sle118/LORA_Sensor/transmitter/334974604_918132536177839_5854289335399050512_n.jpg

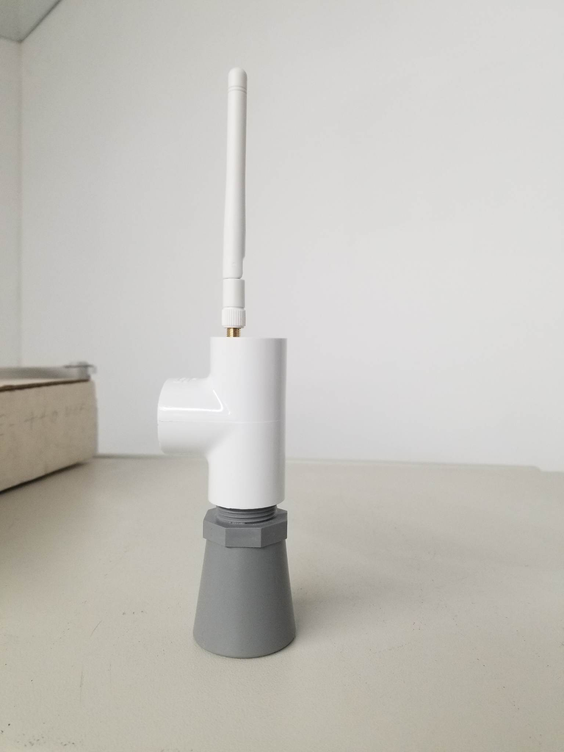
transmitter/334974604_918132536177839_5854289335399050512_n.jpg
