sle118/LORA_Sensor/transmitter/335561218_125201400374179_6329099118651229708_n.jpg

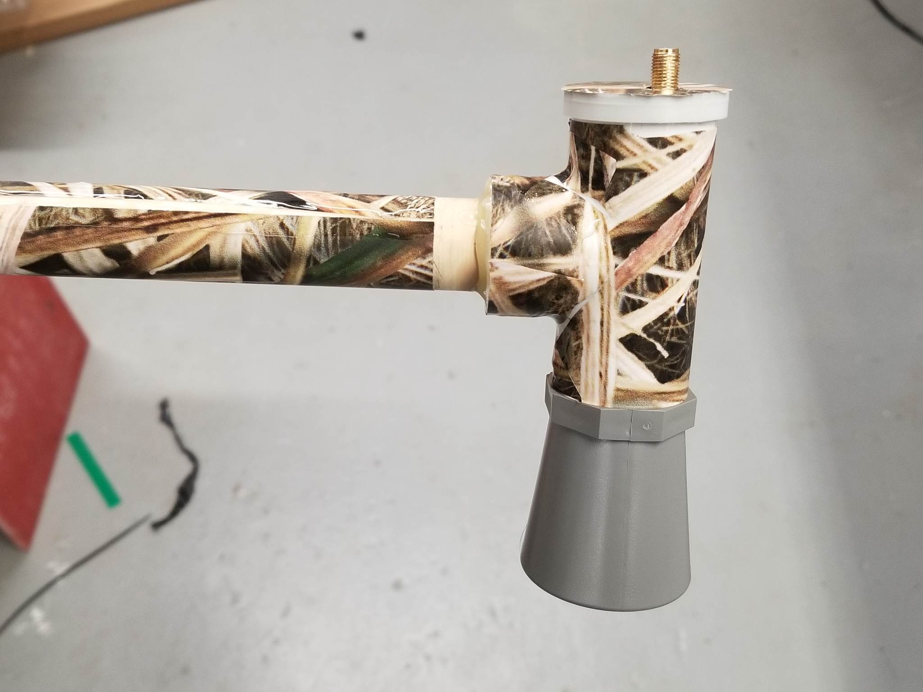
transmitter/335561218_125201400374179_6329099118651229708_n.jpg
