sle118/LORA_Sensor/transmitter/lora_sensor_cap.jpg

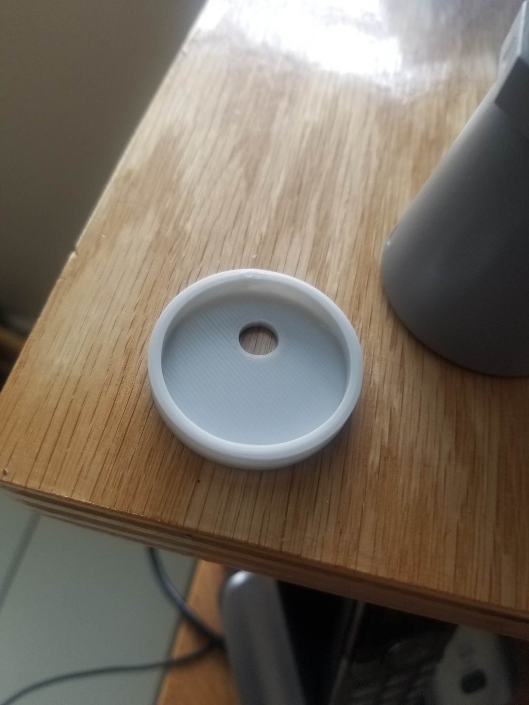
transmitter/lora_sensor_cap.jpg
